gitGNU/gnu_plussydisplay/uc/src/usb.c

/*
	Based on libopencm3-examples/examples/stm32/f4/stm32f4-discovery/usb_cdcacm/cdcacm.c
	Copyright (C) 2010 Gareth McMullin <gareth@blacksphere.co.nz>

	Modifications for Plussy Display
	Copyright (C) 2015  Christian Carlowitz <chca@cmesh.de>

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
	You should have received a copy of the GNU General Public License
	along with this program.  If not, see <http://www.gnu.org/licenses/>.
*/

#include "usb.h"

#include <stdlib.h>
#include <stdio.h>
#include <string.h>
#include <libopencm3/stm32/rcc.h>
#include <libopencm3/stm32/gpio.h>
#include <libopencm3/usb/usbd.h>
#include <libopencm3/usb/cdc.h>
#include <libopencm3/cm3/scb.h>

static const struct usb_device_descriptor dev = {
	.bLength = USB_DT_DEVICE_SIZE,
	.bDescriptorType = USB_DT_DEVICE,
	.bcdUSB = 0x0200,
	.bDeviceClass = USB_CLASS_CDC,
	.bDeviceSubClass = 0,
	.bDeviceProtocol = 0,
	.bMaxPacketSize0 = 64,
	.idVendor = 0x0483,
	.idProduct = 0x5740,
	.bcdDevice = 0x0200,
	.iManufacturer = 1,
	.iProduct = 2,
	.iSerialNumber = 3,
	.bNumConfigurations = 1,
};

/*
 * This notification endpoint isn't implemented. According to CDC spec it's
 * optional, but its absence causes a NULL pointer dereference in the
 * Linux cdc_acm driver.
 */
static const struct usb_endpoint_descriptor comm_endp[] = {{
	.bLength = USB_DT_ENDPOINT_SIZE,
	.bDescriptorType = USB_DT_ENDPOINT,
	.bEndpointAddress = 0x83,
	.bmAttributes = USB_ENDPOINT_ATTR_INTERRUPT,
	.wMaxPacketSize = 16,
	.bInterval = 255,
} };

static const struct usb_endpoint_descriptor data_endp[] = {{
	.bLength = USB_DT_ENDPOINT_SIZE,
	.bDescriptorType = USB_DT_ENDPOINT,
	.bEndpointAddress = 0x01,
	.bmAttributes = USB_ENDPOINT_ATTR_BULK,
	.wMaxPacketSize = 64,
	.bInterval = 1,
}, {
	.bLength = USB_DT_ENDPOINT_SIZE,
	.bDescriptorType = USB_DT_ENDPOINT,
	.bEndpointAddress = 0x82,
	.bmAttributes = USB_ENDPOINT_ATTR_BULK,
	.wMaxPacketSize = 64,
	.bInterval = 1,
} };

static const struct {
	struct usb_cdc_header_descriptor header;
	struct usb_cdc_call_management_descriptor call_mgmt;
	struct usb_cdc_acm_descriptor acm;
	struct usb_cdc_union_descriptor cdc_union;
} __attribute__((packed)) cdcacm_functional_descriptors = {
	.header = {
		.bFunctionLength = sizeof(struct usb_cdc_header_descriptor),
		.bDescriptorType = CS_INTERFACE,
		.bDescriptorSubtype = USB_CDC_TYPE_HEADER,
		.bcdCDC = 0x0110,
	},
	.call_mgmt = {
		.bFunctionLength =
			sizeof(struct usb_cdc_call_management_descriptor),
		.bDescriptorType = CS_INTERFACE,
		.bDescriptorSubtype = USB_CDC_TYPE_CALL_MANAGEMENT,
		.bmCapabilities = 0,
		.bDataInterface = 1,
	},
	.acm = {
		.bFunctionLength = sizeof(struct usb_cdc_acm_descriptor),
		.bDescriptorType = CS_INTERFACE,
		.bDescriptorSubtype = USB_CDC_TYPE_ACM,
		.bmCapabilities = 0,
	},
	.cdc_union = {
		.bFunctionLength = sizeof(struct usb_cdc_union_descriptor),
		.bDescriptorType = CS_INTERFACE,
		.bDescriptorSubtype = USB_CDC_TYPE_UNION,
		.bControlInterface = 0,
		.bSubordinateInterface0 = 1,
	 }
};

static const struct usb_interface_descriptor comm_iface[] = {{
	.bLength = USB_DT_INTERFACE_SIZE,
	.bDescriptorType = USB_DT_INTERFACE,
	.bInterfaceNumber = 0,
	.bAlternateSetting = 0,
	.bNumEndpoints = 1,
	.bInterfaceClass = USB_CLASS_CDC,
	.bInterfaceSubClass = USB_CDC_SUBCLASS_ACM,
	.bInterfaceProtocol = USB_CDC_PROTOCOL_AT,
	.iInterface = 0,

	.endpoint = comm_endp,

	.extra = &cdcacm_functional_descriptors,
	.extralen = sizeof(cdcacm_functional_descriptors)
} };

static const struct usb_interface_descriptor data_iface[] = {{
	.bLength = USB_DT_INTERFACE_SIZE,
	.bDescriptorType = USB_DT_INTERFACE,
	.bInterfaceNumber = 1,
	.bAlternateSetting = 0,
	.bNumEndpoints = 2,
	.bInterfaceClass = USB_CLASS_DATA,
	.bInterfaceSubClass = 0,
	.bInterfaceProtocol = 0,
	.iInterface = 0,

	.endpoint = data_endp,
} };

static const struct usb_interface ifaces[] = {{
	.num_altsetting = 1,
	.altsetting = comm_iface,
}, {
	.num_altsetting = 1,
	.altsetting = data_iface,
} };

static const struct usb_config_descriptor config = {
	.bLength = USB_DT_CONFIGURATION_SIZE,
	.bDescriptorType = USB_DT_CONFIGURATION,
	.wTotalLength = 0,
	.bNumInterfaces = 2,
	.bConfigurationValue = 1,
	.iConfiguration = 0,
	.bmAttributes = 0x80,
	.bMaxPower = 0x32,

	.interface = ifaces,
};

static const char * usb_strings[] = {
	"FSFE Franken",
	"Plussy Display V2",
	"0003",
};

/* Buffer to be used for control requests. */
uint8_t usbd_control_buffer[128];

static int cdcacm_control_request(usbd_device *usbd_dev,
	struct usb_setup_data *req, uint8_t **buf, uint16_t *len,
	void (**complete)(usbd_device *usbd_dev, struct usb_setup_data *req))
{
	(void)complete;
	(void)buf;
	(void)usbd_dev;

	switch (req->bRequest) {
	case USB_CDC_REQ_SET_CONTROL_LINE_STATE: {
		/*
		 * This Linux cdc_acm driver requires this to be implemented
		 * even though it's optional in the CDC spec, and we don't
		 * advertise it in the ACM functional descriptor.
		 */
		return 1;
		}
	case USB_CDC_REQ_SET_LINE_CODING:
		if (*len < sizeof(struct usb_cdc_line_coding)) {
			return 0;
		}

		return 1;
	}
	return 0;
}

#define USB_CMDLEN 256
#define USB_BUFLEN (USB_CMDLEN+2+2)
static char txBuf[USB_BUFLEN];
static char rxBuf[USB_BUFLEN];
static unsigned int rxLen = 0;
static uint8_t rxCnt = 0;
static volatile uint8_t rxReq = 0;
static unsigned int txLen = 0;
//static volatile uint8_t txReq = 0;

#define RX_STATE_STARTOFFRAME 0
#define RX_STATE_LEN 1
#define RX_STATE_DATA 2
static uint8_t rxState = 0;

static void cdcacm_data_rx_cb(usbd_device *usbd_dev, uint8_t ep)
{
	(void)ep;

	char buf[256];
	int len = usbd_ep_read_packet(usbd_dev, 0x01, buf, 256);

	for(int i = 0; i < len; i++)
	{
		switch(rxState)
		{
		case RX_STATE_STARTOFFRAME:
			if(buf[i] == '!')
			{
				rxState = RX_STATE_LEN;
				rxLen = 0;
				rxCnt = 0;
			}
			break;

		case RX_STATE_LEN:
			rxBuf[rxCnt++] = buf[i];
			if(rxCnt == 2)
			{
				sscanf(rxBuf, "%02x", &rxLen);
				if(rxLen>0)
					rxState = RX_STATE_DATA;
				else
					rxState = RX_STATE_STARTOFFRAME;
				rxCnt = 0;
			}
			break;

		case RX_STATE_DATA:
			rxBuf[rxCnt++] = buf[i];
			if(rxCnt == (rxLen+1))
			{
				if((rxBuf[rxLen] == ';') && !rxReq)
				{
					rxReq = 1;
					rxState = RX_STATE_STARTOFFRAME;
				}
				else
				{
					rxState = RX_STATE_STARTOFFRAME;
				}
			}
			break;
		}
	}
}

static void cdcacm_set_config(usbd_device *usbd_dev, uint16_t wValue)
{
	(void)wValue;

	usbd_ep_setup(usbd_dev, 0x01, USB_ENDPOINT_ATTR_BULK, 64,
			cdcacm_data_rx_cb);
	usbd_ep_setup(usbd_dev, 0x82, USB_ENDPOINT_ATTR_BULK, 64, NULL);
	usbd_ep_setup(usbd_dev, 0x83, USB_ENDPOINT_ATTR_INTERRUPT, 16, NULL);

	usbd_register_control_callback(
				usbd_dev,
				USB_REQ_TYPE_CLASS | USB_REQ_TYPE_INTERFACE,
				USB_REQ_TYPE_TYPE | USB_REQ_TYPE_RECIPIENT,
				cdcacm_control_request);
}

static usbd_device *usbd_dev;

void usb_setup(void)
{
	rcc_periph_clock_enable(RCC_GPIOA);
	rcc_periph_clock_enable(RCC_OTGFS);

	gpio_mode_setup(GPIOA, GPIO_MODE_AF, GPIO_PUPD_NONE,
			GPIO9 | GPIO11 | GPIO12);
	gpio_set_af(GPIOA, GPIO_AF10, GPIO9 | GPIO11 | GPIO12);

	usbd_dev = usbd_init(&otgfs_usb_driver, &dev, &config,
			usb_strings, 3,
			usbd_control_buffer, sizeof(usbd_control_buffer));

	usbd_register_set_config_callback(usbd_dev, cdcacm_set_config);
}

void usb_poll(void)
{
	usbd_poll(usbd_dev);
}

uint8_t usb_rx_ready(void)
{
	return rxReq;
}

int usb_get_read(char* str, uint16_t maxlen)
{
	for(int i = 0; (i < maxlen) && (i < (uint8_t)rxLen); i++)
	{
		*str = rxBuf[i];
		str++;
	}
	*str = 0;
	int tmp = rxLen;
	rxReq = 0;
	return tmp;
}

void usb_write(char* str)
{
	unsigned int len = strlen(str);
	sprintf(txBuf, "@%02x", len);
	int i = 3;
	txLen = 0;
	while(*str != 0)
	{
		txBuf[i++] = *str;
		str++;
	}
	txBuf[i++] = ';';
	txLen = len+4;

	int offs = 0;
	while(txLen > 0)
	{
		if(txLen > 64)
		{
			while (usbd_ep_write_packet(usbd_dev, 0x82, txBuf+offs, 64) == 0);
			txLen -= 64;
			offs += 64;
		}
		else
		{
			while (usbd_ep_write_packet(usbd_dev, 0x82, txBuf+offs, txLen) == 0);
			txLen = 0;
		}
	}

}
